tabakovKonstantin/zigbee-watermeter/main/zigbee_app.h

#pragma once

#include <stdbool.h>

#include "esp_err.h"

bool zigbee_app_is_joined(void);
void zigbee_app_report_sensor_pulse(void);
void zigbee_app_set_ota_active(bool active);
esp_err_t zigbee_app_start(void);
